khill25/Dreamdrive/Dreamcast/sw/rp2040/mcu2/mcu2.c

/**
 * SPDX-License-Identifier: BSD-2-Clause
 *
 * Copyright (c) 2023 Kaili Hill
 */

#include <stdio.h>

#include "pico/stdlib.h"
#include "hardware/pio.h"
#include "hardware/vreg.h"

#include "interconnect_mux.pio.h"

#define IDE_DATABUS_MASK 				(0xFFFF) 	// pins 0-15

#define INTERCONNECT_DATABUS_MASK 		(0xFF0000) 	// pins 16-23
#define INTERCONNECT_BUS_DIRECTION_MASK (0x1000000) // pin 24
#define INTERCONNECT_IRQ_LOW_MASK		(0x4000000) // pin 26
#define INTERCONNECT_IRQ_HIGH_MASK 		(0x8000000) // pin 27
#define INTERCONNECT_IRQ_LOW_PIN		(24)
#define INTERCONNECT_IRQ_HIGH_PIN		(25)

#define INTERCONNECT_BUS_OUTPUT_LOW_SM 		(0)
#define INTERCONNECT_BUS_OUTPUT_HIGH_SM 	(1)
#define INTERCONNECT_BUS_INPUT_LOW_SM 		(2)
#define INTERCONNECT_BUS_INPUT_HIGH_SM 		(3)
#define INTERCONNECT_READ_FROM_DREAMCAST_SM (2)

#define INTERCONNECT_MCU_PIN_START 			(16)
#define INTERCONNECT_BUS_PIN_LOW_START 		(0)
#define INTERCONNECT_BUS_PIN_HIGH_START 	(8)
#define INTERCONNECT_BUS_PIN_LOW_PIN_COUNT 	(8)
#define INTERCONNECT_BUS_PIN_HIGH_PIN_COUNT (8)

void setup_read_from_dreamcast() {
	uint sm = 0;
	uint offset = pio_add_program(pio0, &read_from_dreamcast_program);
	pio_sm_config c = read_from_dreamcast_program_get_default_config(offset);

	sm_config_set_in_pins(&c, 0);
	sm_config_set_out_pins(&c, 16, 8);

	pio_sm_set_pindirs_with_mask(pio0, sm, 0xFF0000, 0xFFFFFF);

	sm_config_set_in_shift(&c, false, false, 16);

	pio_sm_init(pio0, sm, offset, &c);
}

void setup_write_to_dreamcast() {
	uint sm = 1;
	uint offset = pio_add_program(pio0, &write_to_dreamcast_program);
	pio_sm_config c = write_to_dreamcast_program_get_default_config(offset);

	// Input pins start at pin 16
	sm_config_set_in_pins(&c, 16);

	// Output pins are 0-15, but this is the low byte so start at pin 0
	sm_config_set_out_pins(&c, 0, 16);
	
	// Still set the initial pins to be read
	pio_sm_set_pindirs_with_mask(pio0, sm, 0xFF0000, 0xFFFFFF);
	
	sm_config_set_in_shift(&c, false, false, 8);

	pio_sm_init(pio0, sm, offset, &c);
}

// void setup_read_write_combined_program() {
// 	uint sm = 0;
// 	uint offset = pio_add_program(pio0, &mcu_databus_read_write_program);
// 	pio_sm_config c = mcu_databus_read_write_program_get_default_config(offset);

// 	// Input pins start at pin 0
// 	sm_config_set_in_pins(&c, 0);

// 	// Output pins are 0-15, but this is the low byte so start at pin 0
// 	sm_config_set_out_pins(&c, 0, 24);
	
// 	// Set all pins input
// 	pio_sm_set_pindirs_with_mask(pio0, sm, 0x00000000, 0x00FFFFFF);

// 	// SET JMP PIN!!!!!!!!!!!!!
// 	sm_config_set_jmp_pin(&c, 27);
	
// 	sm_config_set_in_shift(&c, false, false, 8);

// 	pio_sm_init(pio0, sm, offset, &c);
// }

void setup_interconnect() {

	// init all the pins used by pio
	for(int i = 0; i < 24; i++) {
		pio_gpio_init(pio0, i);
	}

	// pio_gpio_init(pio0, 27);

	// setup_read_write_combined_program();
	setup_read_from_dreamcast();
	setup_write_to_dreamcast();
	pio_sm_set_enabled(pio0, 0, true);
	pio_sm_set_enabled(pio0, 1, true);
}

// When interconnect is output(output to dreamcast), OUTPUT data from mcu TO BUS
// When interconnect is input (input from dreamcast), OUTPUT data from bus TO MCU
volatile bool read_from_dreamcast = false;

// static inline void swap_direction() {
// 	// if (read_from_dreamcast) {
// 	// 	pio1->ctrl = 0x33; // read from dreamcast
// 	// } else {
// 	// 	pio1->ctrl = 0x44; // send to dreamcast
// 	// }
// 	// pio_restart_sm_mask(pio1, 0x3);

// 	pio_sm_set_enabled(pio0, 0, true);
// 	pio_sm_set_enabled(pio0, 1, true);
// }

int main(void) {
	stdio_init_all();
	// current_mcu = MCU2;

	for(int i = 0; i < 16; i++) {
		gpio_init(i);
		gpio_set_function(i, GPIO_FUNC_PIO0);
	}

	for(int i = 16; i < 24; i++) {
		gpio_init(i);
		gpio_set_dir(i, GPIO_IN);
	}

	const int freq_khz = 266000;
	// const int freq_khz = 336000;
	// vreg_set_voltage(VREG_VOLTAGE_1_25);
	bool clockWasSet = set_sys_clock_khz(freq_khz, false);

	gpio_init(INTERCONNECT_IRQ_LOW_PIN);
	gpio_set_dir(INTERCONNECT_IRQ_LOW_PIN, GPIO_IN);
	gpio_set_pulls(INTERCONNECT_IRQ_LOW_PIN, false, true);

	gpio_init(INTERCONNECT_IRQ_HIGH_PIN);
	gpio_set_dir(INTERCONNECT_IRQ_HIGH_PIN, GPIO_IN);
	gpio_set_pulls(INTERCONNECT_IRQ_HIGH_PIN, false, true);

	setup_interconnect();
	volatile uint32_t pins = 0;

	while(1) {
		tight_loop_contents();
		// current_direction = gpio_get(INTERCONNECT_DIRECTION_PIN);
		// if (current_direction != read_from_dreamcast) {
		// 	read_from_dreamcast = current_direction;
		// 	swap_direction();
		// }

		// pins = pio_sm_get_blocking(pio0, 0);
		// printf("%x\n", pins);
	}
}
