khill25/Dreamdrive/Dreamcast/sw/rp2040/shared/pio_uart/pio_uart.c

/**
 * SPDX-License-Identifier: BSD-2-Clause
 *
 * Copyright (c) 2022 Kaili Hill
 */
#include <stdio.h>
#include <stdint.h>
#include <stdbool.h>
#include "shared.h"
#include "pio_uart.h"
#include "pico/stdlib.h"

pio_uart_inst_t uart_rx = {
        .pio = pio1,
        .sm = 0 //joybus and rx both share the same state machine. Disable rx before starting joybus
};

pio_uart_inst_t uart_tx = {
        .pio = pio1,
        .sm = 1
};

RXRingBuffer_t rxRingBuffer = {};
void rx_uart_interrupt() {
    while(uart_rx_program_is_readable()) {
        char c = uart_rx_program_getc();
        rxRingBuffer.buf[rxRingBuffer.head++] = c;
        if (rxRingBuffer.head == RX_RING_BUFFER_SIZE) {
            rxRingBuffer.head = 0;
        }
    }
}

bool rx_uart_buffer_has_data() {
    return rxRingBuffer.tail != rxRingBuffer.head;
}

uint8_t rx_uart_buffer_get() {
    uint8_t ret = rxRingBuffer.buf[rxRingBuffer.tail++];
    if (rxRingBuffer.tail >= RX_RING_BUFFER_SIZE) {
        rxRingBuffer.tail = 0;
    }
    return ret;
}

void rx_uart_buffer_reset() {
    rxRingBuffer.head = 0;
    rxRingBuffer.tail = 0;
}

uint pioUartRXOffset = 0;
uint pioUartTXOffset = 0;
uint8_t isUartTXRunning = false;
uint8_t isUartRXRunning = false;

void pio_uart_init(int rxPin, int txPin) {
    uint divider = 8; // Clock divider

    if (rxPin >= 0) {
	    pioUartRXOffset = pio_add_program(uart_rx.pio, &uart_rx_program);
        uart_rx_program_init(uart_rx.pio, uart_rx.sm, pioUartRXOffset, rxPin, divider);
        isUartRXRunning = true;
        // Finally, set irq for rx
        irq_set_exclusive_handler(PIO1_IRQ_0, rx_uart_interrupt);
	    pio_set_irq0_source_enabled(pio1, pis_sm0_rx_fifo_not_empty, true);
        irq_set_enabled(PIO1_IRQ_0, true);
    }

    if (txPin >= 0) {
	    pioUartTXOffset = pio_add_program(uart_tx.pio, &uart_tx_program);
        uart_tx_program_init(uart_tx.pio, uart_tx.sm, pioUartTXOffset, txPin, divider);
        isUartTXRunning = true;
    }
}

void pio_uart_stop(bool tx, bool rx) {
    if (tx) {
        isUartTXRunning = false;
        pio_sm_set_enabled(uart_tx.pio, uart_tx.sm, false);
        pio_remove_program(uart_tx.pio, &uart_tx_program, pioUartTXOffset);
    }

    if (rx) {
        isUartRXRunning = false;
        pio_sm_set_enabled(uart_rx.pio, uart_rx.sm, false);
        pio_remove_program(uart_rx.pio, &uart_rx_program, pioUartRXOffset);
        irq_set_enabled(PIO1_IRQ_0, false);
        pio_set_irq0_source_enabled(pio1, pis_sm0_rx_fifo_not_empty, false);
        irq_remove_handler(PIO1_IRQ_0, rx_uart_interrupt);
    }
}

void uart_tx_program_putc(char c) {
    if (!isUartTXRunning) { return; }
    pio_sm_put_blocking(uart_tx.pio, uart_tx.sm, (uint32_t)c);
}

void uart_tx_program_puts(const char *s) {
    if (!isUartTXRunning) { return; }
    while (*s)
        uart_tx_program_putc(*s++);
}

char uart_rx_program_getc() {
    if (!isUartRXRunning) { return 0; }

    // 8-bit read from the uppermost byte of the FIFO, as data is left-justified
    io_rw_8 *rxfifo_shift = (io_rw_8*)&uart_rx.pio->rxf[uart_rx.sm] + 3;
    while (pio_sm_is_rx_fifo_empty(uart_rx.pio, uart_rx.sm))
        tight_loop_contents();
    return (char)*rxfifo_shift;
}

// If there is data in the rx fifo, then return true
bool uart_rx_program_is_readable() {
    if (!isUartRXRunning) { return false; }
    return !pio_sm_is_rx_fifo_empty(uart_rx.pio, uart_rx.sm);
}

bool uart_tx_program_is_writable() {
    if (!isUartTXRunning) { return false; }
    return !pio_sm_is_tx_fifo_full(uart_tx.pio, uart_tx.sm);
}

void inter_mcu_comms_test() {
    int testSize = 1023;// * 1024 * 1; // 1MB
    uint32_t startTime = time_us_32();
    for(int i = 0; i < testSize; i++) {
        while(!uart_tx_program_is_writable()) { tight_loop_contents(); }
        uart_tx_program_putc(i);
    }
    uint32_t totalTime = time_us_32() - startTime;
    float totalSeconds = (((float)totalTime) / 1000.0f / 1000.0f);
    float mbs = (1.0f / 1024.0f) / (totalSeconds);
    printf("Sent 1MB in %dus, %dms, %fMB/s\n", totalTime, totalTime / 1000, mbs);
}
