khill25/Dreamdrive/Dreamcast/sw/rp2040/shared/pio_uart/pio_uart.h

/**
 * SPDX-License-Identifier: BSD-3-Clause
 *
 * Copyright (c) 2022 Kaili Hill
 */

#ifndef _PIO_UART_H
#define _PIO_UART_H

#include "hardware/pio.h"
#include "pio_uart.pio.h"

typedef struct pio_uart_inst {
    PIO pio;
    uint sm;
} pio_uart_inst_t;

bool rx_uart_buffer_has_data();
uint8_t rx_uart_buffer_get();
void rx_uart_buffer_reset();

// Use the rxRingBuffer to read from the uart
// Pass -1 to not enable that program
void pio_uart_init(int rxPin, int txPin);

// pass true to stop, and false to do nothing
void pio_uart_stop(bool tx, bool rx);

void uart_tx_program_putc(char c);
void uart_tx_program_puts(const char *s);
char uart_rx_program_getc();
bool uart_rx_program_is_readable();
bool uart_tx_program_is_writable();

void inter_mcu_comms_test();

#endif
