khill25/Dreamdrive/Dreamcast/sw/rp2350/gdrom.h

// GDROM magic variables and data

#pragma once



// Canned replies for certain commands below

uint16_t reply_a1[] = 
{
	0x2020,0x0020,0x0000,0x0000,0x0000,0x0000,0x0000,0x0000,
	0x4553,0x2020,0x2020,0x2020,0x2020,0x2020,0x2020,0x2020,
	0x4443,0x522d,0x4d4f,0x4420,0x4952,0x4556,0x2020,0x2020,
	0x2e36,0x3334,0x0000,0x0000,0x0000,0x0000,0x0000,0x0000,
	0x0000,0x0000,0x0000,0x0000,0x0000,0x0000,0x0000,0x0000
};

uint16_t reply_11[] = 
{
	0x0000,0x0000,0xb400,0x0019,0x0800,0x4553,0x2020,0x2020,
	0x2020,0x6552,0x2076,0x2e36,0x3334,0x3939,0x3430,0x3830
};

uint16_t reply_71[] = 
{
		0x0b96,0xf045,0xff7e,0x063d,0x7d4d,0xbf10,0x0007,0xcf73,0x009c,0x0cbc,0xaf1c,0x301c,0xa7e7,0xa803,0x0098,0x0fbd,0x5bbd,0x50aa,0x3923,
		0x1031,0x690e,0xe513,0xd200,0x660d,0xbf54,0xfd5f,0x7437,0x5bf4,0x0022,0x09c6,0xca0f,0xe893,0xaba4,0x6100,0x2e0e,0x4be1,0x8b76,0xa56a,
		0xe69c,0xc423,0x4b00,0x1b06,0x0191,0xe200,0xcf0d,0x38ca,0xb93a,0x91e7,0xefe5,0x004b,0x09d6,0x68d3,0xc43e,0x2daf,0x2a00,0xf90d,0x78fc,
		0xaeed,0xb399,0x5a32,0x00e7,0x0a4c,0x9722,0x825b,0x7a06,0x004c,0x0e42,0x7857,0xf546,0xfc20,0xcb6b,0x5b01,0x0086,0x0ee4,0x26b2,0x71cd,
		0xa5e3,0x0633,0x9a8e,0x0050,0x0707,0x34f5,0xe6ef,0x3200,0x130f,0x5941,0x0f56,0x3802,0x642a,0x072a,0x003e,0x1152,0x1d2a,0x765f,0xa066,
		0x2fb2,0xc797,0x6e5e,0xe252,0x5800,0xca09,0xa589,0x0adf,0x00de,0x0650,0xb849,0x00b4,0x0577,0xe824,0xbb00,0x910c,0xa289,0x628b,0x6ade,
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
	0xba, 0x06, 0x0d, 0xca, 0x6a, 0x1f
};

// static const uint16_t cmd71_reply[] = {
// 	0x06ba, 0xca0d, 0x1f6a
// };


uint32_t reply_71_sz=sizeof(reply_71);
char szExDT[8][32] =
{
	"Any...",
	"CD-DA",
	"Mode1",
	"Mode2",
	"Mode2-Form1",
	"Mode2-Form2",
	"Mode2-Non-XA",
	"-> GD UNKNOWN TYPE <="
};
