khill25/Dreamdrive/N64/sw/dreamdrive64/debug.h

/**
 * SPDX-License-Identifier: BSD-2-Clause
 *
 * Copyright (c) 2023 Kaili Hill
 */

/*
 * Collection of debug flags and functions.  
 * Not yet in use but should help clean up a bunch of the code.
 * 
 */

#pragma once

#define MCU2_LOAD_ROM 0
#define MCU1_USE_LOADED_ROM 0
