khill25/Dreamdrive/Dreamcast/sw/rp2350/utils/gdrom_utils.h

#pragma once

#include "common.h"

/*
 * read data from the sd card using params from the SPI command packets
 * This could probably just be part of sega_packet_interface.c/h but we can evaluate that later
 * 
 */


extern uint8_t gdrom_read_buffer[MAX_BUFFER_SIZE]; // This is about 74KB of ram
extern uint8_t gdrom_read_buffer2[MAX_BUFFER_SIZE]; // This is about 74KB of ram
extern uint16_t* gdrom_16bit_buffer_ptr;

extern uint8_t gdrom_read_data_select_value;
extern uint8_t gdrom_read_expected_data_type;
extern uint8_t gdrom_read_data_parameter_type; // 0 = FAD or 1 =MSF

extern uint32_t gdrom_read_start_sector;
extern uint32_t gdrom_read_read_sectors; // Used by fill buffer to offset another preload
extern uint32_t gdrom_read_remaining_sectors;
extern uint32_t gdrom_read_sector_size;
extern uint32_t gdrom_read_buffer_index;
extern uint32_t gdrom_read_buffer_size; // how much data is actually in here

extern uint32_t gdrom_read_current_byte_count;
extern uint32_t gdrom_read_bytes_remanining_in_sector;
extern uint32_t gdrom_read_bytes_remanining;

// Not sure I need to keep track of any of this as it's done in the nulldc code
// enum cd_read_data_select_type {
//     CD_READ_HEADER = 0,
//     CD_READ_SUBHEADER = 1,
//     CD_READ_DATA = 2,
//     CD_READ_OTHER = 3 // all bytes of the sector are output (2352)

//     // If data type is CD_DA, this field is ignored and transfers 2352 bytes
// };

// enum cd_read_expected_data_type {
//     CD_READ_DATA_TYPE_ANY = 0b000,
//     CD_READ_DATA_TYPE_CD_DA = 0b001,
//     CD_READ_DATA_TYPE_MODE_1 = 0b010,
//     CD_READ_DATA_TYPE_MODE_2 = 0b011,
//     CD_READ_DATA_TYPE_MODE_2_FORM_1 = 0b100,
//     CD_READ_DATA_TYPE_MODE_2_FORM_2 = 0b101,
//     CD_READ_DATA_TYPE_MODE_2_NON_XA = 0b110
// };

// struct {
//     cd_read_data_select_type dataSelect;
//     cd_read_expected_data_type expectedDataType;
//     bool isFAD;
//     uint32_t startAddress;
//     uint32_t transferLength;
// } cd_read_params;

// struct {
//     uint32_t sectorSize;
//     uint32_t sectorStart;
//     uint32_t sectorEnd;
//     uint32_t currentSector;

//     uint32_t currentBufferPosition; // in bytes
    
// } cd_read_state;

// Read and process the disc image
void gdrom_read_default_disc_image();

// Call at the start of a cd_read command to setup state variables and init the read buffer
void gdrom_read_start(uint8_t* packet, bool isDMA);

// Pass in the ata data register to write the data to
// Returns false if there is no more data to read
// Returns true if the buffer still has requested data remaining
bool gdrom_read_consume_buffer(uint16_t* toBuffer);

// Read sectors and put them in the buffer
// Another helper method that probably doesn't need to be called directly
// Unless we swap to reading a sector at a time
void gdrom_read_sectors(uint8_t* buffer, uint32_t sector, uint32_t sectorCount, uint32_t sectorSize);

// Used as a helper function to fill the read buffer with data from the disc
// Probably dont need to call this method as it's called from gdrom_read_start
void gdrom_fill_read_buffer(uint8_t* buffer);

static uint8_t gdrom_rom_data[] =
{
	0x96, 0x0B, 0x45, 0xF0, 0x7E, 0xFF, 0x3D, 0x06,
	0x4D, 0x7D, 0x10, 0xBF, 0x07, 0x00, 0x73, 0xCF,
	0x9C, 0x00, 0xBC, 0x0C, 0x1C, 0xAF, 0x1C, 0x30,
	0xE7, 0xA7, 0x03, 0xA8, 0x98, 0x00, 0xBD, 0x0F,
	0xBD, 0x5B, 0xAA, 0x50, 0x23, 0x39, 0x31, 0x10,
	0x0E, 0x69, 0x13, 0xE5, 0x00, 0xD2, 0x0D, 0x66,
	0x54, 0xBF, 0x5F, 0xFD, 0x37, 0x74, 0xF4, 0x5B,
	0x22, 0x00, 0xC6, 0x09, 0x0F, 0xCA, 0x93, 0xE8,
	0xA4, 0xAB, 0x00, 0x61, 0x0E, 0x2E, 0xE1, 0x4B,
	0x76, 0x8B, 0x6A, 0xA5, 0x9C, 0xE6, 0x23, 0xC4,
	0x00, 0x4B, 0x06, 0x1B, 0x91, 0x01, 0x00, 0xE2,
	0x0D, 0xCF, 0xCA, 0x38, 0x3A, 0xB9, 0xE7, 0x91,
	0xE5, 0xEF, 0x4B, 0x00, 0xD6, 0x09, 0xD3, 0x68,
	0x3E, 0xC4, 0xAF, 0x2D, 0x00, 0x2A, 0x0D, 0xF9,
	0xFC, 0x78, 0xED, 0xAE, 0x99, 0xB3, 0x32, 0x5A,
	0xE7, 0x00, 0x4C, 0x0A, 0x22, 0x97, 0x5B, 0x82,
	0x06, 0x7A, 0x4C, 0x00, 0x42, 0x0E, 0x57, 0x78,
	0x46, 0xF5, 0x20, 0xFC, 0x6B, 0xCB, 0x01, 0x5B,
	0x86, 0x00, 0xE4, 0x0E, 0xB2, 0x26, 0xCD, 0x71,
	0xE3, 0xA5, 0x33, 0x06, 0x8E, 0x9A, 0x50, 0x00,
	0x07, 0x07, 0xF5, 0x34, 0xEF, 0xE6, 0x00, 0x32,
	0x0F, 0x13, 0x41, 0x59, 0x56, 0x0F, 0x02, 0x38,
	0x2A, 0x64, 0x2A, 0x07, 0x3E, 0x00, 0x52, 0x11,
	0x2A, 0x1D, 0x5F, 0x76, 0x66, 0xA0, 0xB2, 0x2F,
	0x97, 0xC7, 0x5E, 0x6E, 0x52, 0xE2, 0x00, 0x58,
	0x09, 0xCA, 0x89, 0xA5, 0xDF, 0x0A, 0xDE, 0x00,
	0x50, 0x06, 0x49, 0xB8, 0xB4, 0x00, 0x77, 0x05,
	0x24, 0xE8, 0x00, 0xBB, 0x0C, 0x91, 0x89, 0xA2,
	0x8B, 0x62, 0xDE, 0x6A, 0xC6, 0x60, 0x00, 0xE7,
	0x0F, 0x0F, 0x11, 0x96, 0x55, 0xD2, 0xBF, 0xE6,
	0x48, 0x0B, 0x5C, 0xAB, 0xDC, 0x00, 0xBA, 0x0A,
	0x30, 0xD7, 0x48, 0x0E, 0x78, 0x63, 0x0C, 0x00,
	0xD2, 0x0D, 0xFB, 0x8A, 0xA3, 0xFE, 0xF8, 0x3A,
	0xDD, 0x88, 0xA9, 0x4B, 0x00, 0xA2, 0x0A, 0x75,
	0x5D, 0x0D, 0x37, 0x24, 0xC5, 0x9D, 0x00, 0xF7,
	0x0B, 0x25, 0xEF, 0xDB, 0x41, 0xE0, 0x52, 0x3E,
	0x4E, 0x00, 0xB7, 0x03, 0x00, 0xE5, 0x11, 0xB9,
	0xDE, 0x5A, 0x57, 0xCF, 0xB9, 0x1A, 0xFC, 0x7F,
	0x26, 0xEE, 0x7B, 0xCD, 0x2B, 0x00, 0x4B, 0x08,
	0xB8, 0x09, 0x70, 0x6A, 0x9F, 0x00, 0x4B, 0x11,
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
};
